volzotan/LensLeech/media/2678_output_3_i-1725881.png

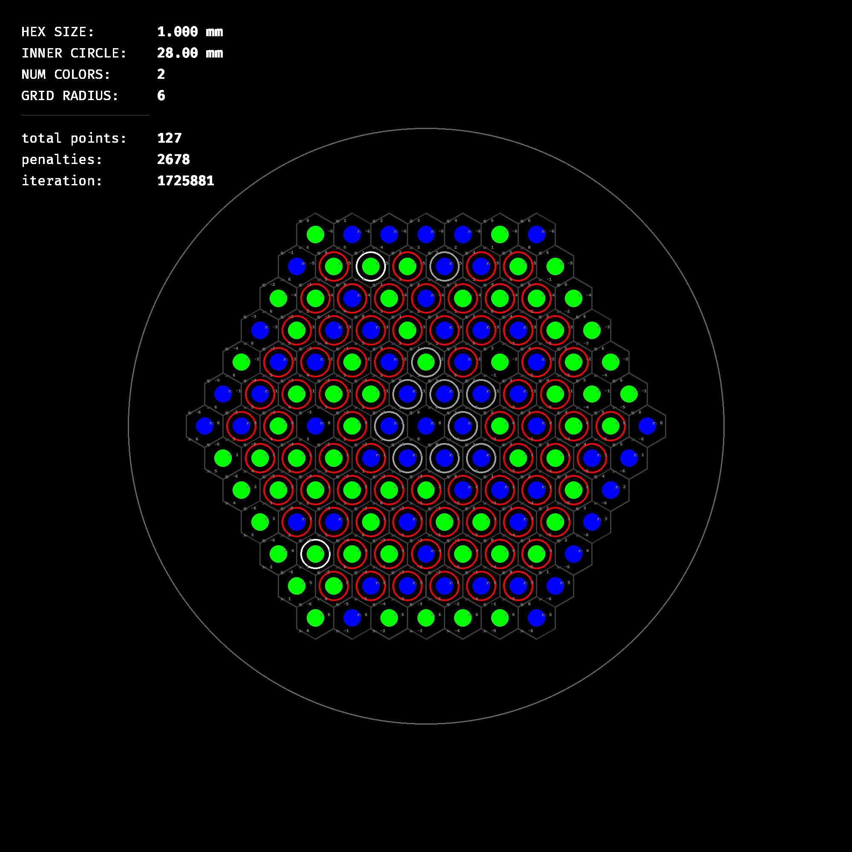
media/2678_output_3_i-1725881.png
