volzotan/LensLeech/pattern/2633_output_0_i-1303443.png

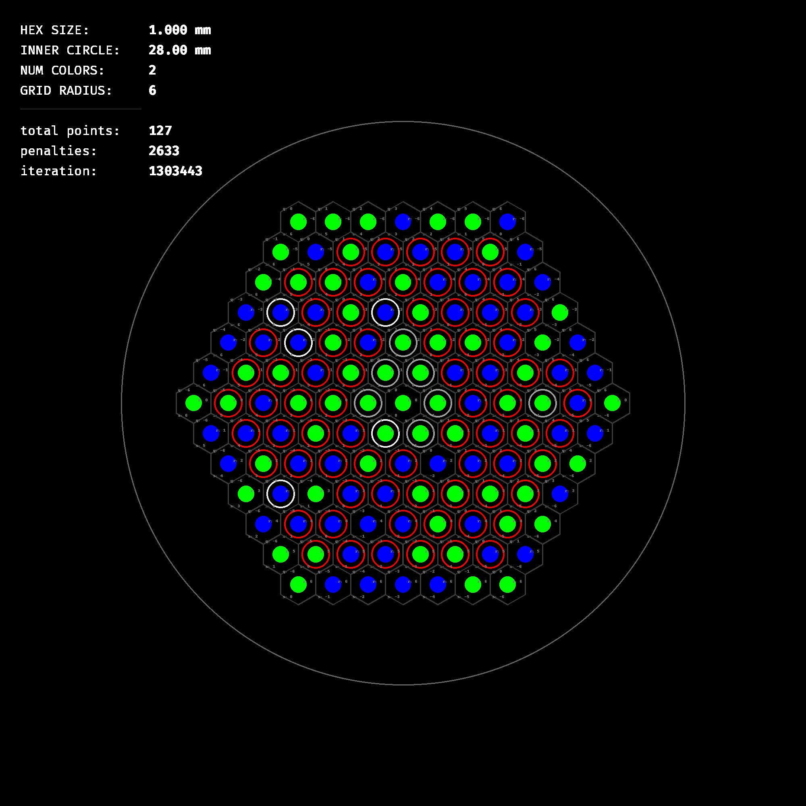
pattern/2633_output_0_i-1303443.png
